2484874936/keyboard/software/groundwork/bsp_flash/bsp_flash.c

/*MIT License

Copyright (c) 2020 SEASKY-Master

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
THE SOFTWARE IS PROVIDED "AS IS", WITHOUT WARRANTY OF ANY KIND, EXPRESS OR
IMPLIED, INCLUDING BUT NOT LIMITED TO THE WARRANTIES OF MERCHANTABILITY,
FITNESS FOR A PARTICULAR PURPOSE AND NONINFRINGEMENT. IN NO EVENT SHALL THE
AUTHORS OR COPYRIGHT HOLDERS BE LIABLE FOR ANY CLAIM, DAMAGES OR OTHER
LIABILITY, WHETHER IN AN ACTION OF CONTRACT, TORT OR OTHERWISE, ARISING FROM,
OUT OF OR IN CONNECTION WITH THE SOFTWARE OR THE USE OR OTHER DEALINGS IN THE
SOFTWARE.
*/

#include "bsp_flash.h"
#include "main.h"
#include "string.h"

static uint32_t ger_sector(uint32_t address);


/**
  * @brief          擦除flash
  * @param[in]      address: flash 地址
  * @param[in]      len: 页数量
  * @retval         none
  */
void flash_erase_address(uint32_t address, uint16_t len)
{
    FLASH_EraseInitTypeDef flash_erase;
    uint32_t error;

    flash_erase.Sector = ger_sector(address);
    flash_erase.TypeErase = FLASH_TYPEERASE_SECTORS;
    flash_erase.VoltageRange = FLASH_VOLTAGE_RANGE_3;
    flash_erase.NbSectors = len;

    HAL_FLASH_Unlock();
    HAL_FLASHEx_Erase(&flash_erase, &error);
    HAL_FLASH_Lock();
}


/**
  * @brief          往一页flash写数据
  * @param[in]      start_address: flash 地址
  * @param[in]      buf: 数据指针
  * @param[in]      len: 数据长度
  * @retval         success 0, fail -1
  */
int8_t flash_write_single_address(uint32_t start_address, uint32_t *buf, uint32_t len)
{
    static uint32_t uw_address;
    static uint32_t end_address;
    static uint32_t *data_buf;
    static uint32_t data_len;

    HAL_FLASH_Unlock();

    uw_address = start_address;
    end_address = get_next_flash_address(start_address);
    data_buf = buf;
    data_len = 0;

    while (uw_address <= end_address)
    {

        if (HAL_FLASH_Program(FLASH_TYPEPROGRAM_WORD,uw_address, *data_buf) == HAL_OK)
        {
            uw_address += 4;
            data_buf++;
            data_len++;
            if (data_len == len)
            {
                break;
            }
        }
        else
        {
            HAL_FLASH_Lock();
            return -1;
        }
    }

    HAL_FLASH_Lock();
    return 0;
}


/**
  * @brief          往几页flash写数据
  * @param[in]      start_address: flash 开始地址
  * @param[in]      end_address: flash 结束地址
  * @param[in]      buf: 数据指针
  * @param[in]      len: 数据长度
  * @retval         success 0, fail -1
  */
int8_t flash_write_muli_address(uint32_t start_address, uint32_t end_address, uint32_t *buf, uint32_t len)
{
    uint32_t uw_address = 0;
    uint32_t *data_buf;
    uint32_t data_len;

    HAL_FLASH_Unlock();

    uw_address = start_address;
    data_buf = buf;
    data_len = 0;
    while (uw_address <= end_address)
    {
        if (HAL_FLASH_Program(FLASH_TYPEPROGRAM_WORD,uw_address, *data_buf) == HAL_OK)
        {
            uw_address += 4;
            data_buf++;
            data_len++;
            if (data_len == len)
            {
                break;
            }
        }
        else
        {
            HAL_FLASH_Lock();
            return -1;
        }
    }

    HAL_FLASH_Lock(); 
    return 0;
}



/**
  * @brief          从flash读数据
  * @param[in]      start_address: flash 地址
  * @param[out]     buf: 数据指针
  * @param[in]      len: 数据长度
  * @retval         none
  */
void flash_read(uint32_t address, uint32_t *buf, uint32_t len)
{
    memcpy(buf, (void*)address, len *4);
}


/**
  * @brief          获取flash的sector号
  * @param[in]      address: flash 地址
  * @retval         sector号
  */
uint32_t ger_sector(uint32_t address)
{
    uint32_t sector = 0;
    if ((address < ADDR_FLASH_SECTOR_1) && (address >= ADDR_FLASH_SECTOR_0))
    {
        sector = FLASH_SECTOR_0;
    }
    else if ((address < ADDR_FLASH_SECTOR_2) && (address >= ADDR_FLASH_SECTOR_1))
    {
        sector = FLASH_SECTOR_1;
    }
    else if ((address < ADDR_FLASH_SECTOR_3) && (address >= ADDR_FLASH_SECTOR_2))
    {
        sector = FLASH_SECTOR_2;
    }
    else if ((address < ADDR_FLASH_SECTOR_4) && (address >= ADDR_FLASH_SECTOR_3))
    {
        sector = FLASH_SECTOR_3;
    }
    else if ((address < ADDR_FLASH_SECTOR_5) && (address >= ADDR_FLASH_SECTOR_4))
    {
        sector = FLASH_SECTOR_4;
    }
    else if ((address < ADDR_FLASH_SECTOR_6) && (address >= ADDR_FLASH_SECTOR_5))
    {
        sector = FLASH_SECTOR_5;
    }
    else if ((address < ADDR_FLASH_SECTOR_7) && (address >= ADDR_FLASH_SECTOR_6))
    {
        sector = FLASH_SECTOR_6;
    }
    else if ((address < ADDR_FLASH_SECTOR_8) && (address >= ADDR_FLASH_SECTOR_7))
    {
        sector = FLASH_SECTOR_7;
    }
    else if ((address < ADDR_FLASH_SECTOR_9) && (address >= ADDR_FLASH_SECTOR_8))
    {
        sector = FLASH_SECTOR_8;
    }
    else if ((address < ADDR_FLASH_SECTOR_10) && (address >= ADDR_FLASH_SECTOR_9))
    {
        sector = FLASH_SECTOR_9;
    }
    else if ((address < ADDR_FLASH_SECTOR_11) && (address >= ADDR_FLASH_SECTOR_10))
    {
        sector = FLASH_SECTOR_10;
    }
    else if ((address < ADDR_FLASH_SECTOR_12) && (address >= ADDR_FLASH_SECTOR_11))
    {
        sector = FLASH_SECTOR_11;
    }
    else
    {
        sector = FLASH_SECTOR_11;
    }

    return sector;
}


/**
  * @brief          获取下一页flash地址
  * @param[in]      address: flash 地址
  * @retval         下一页flash地址
  */
uint32_t get_next_flash_address(uint32_t address)
{
    uint32_t sector = 0;

    if ((address < ADDR_FLASH_SECTOR_1) && (address >= ADDR_FLASH_SECTOR_0))
    {
        sector = ADDR_FLASH_SECTOR_1;
    }
    else if ((address < ADDR_FLASH_SECTOR_2) && (address >= ADDR_FLASH_SECTOR_1))
    {
        sector = ADDR_FLASH_SECTOR_2;
    }
    else if ((address < ADDR_FLASH_SECTOR_3) && (address >= ADDR_FLASH_SECTOR_2))
    {
        sector = ADDR_FLASH_SECTOR_3;
    }
    else if ((address < ADDR_FLASH_SECTOR_4) && (address >= ADDR_FLASH_SECTOR_3))
    {
        sector = ADDR_FLASH_SECTOR_4;
    }
    else if ((address < ADDR_FLASH_SECTOR_5) && (address >= ADDR_FLASH_SECTOR_4))
    {
        sector = ADDR_FLASH_SECTOR_5;
    }
    else if ((address < ADDR_FLASH_SECTOR_6) && (address >= ADDR_FLASH_SECTOR_5))
    {
        sector = ADDR_FLASH_SECTOR_6;
    }
    else if ((address < ADDR_FLASH_SECTOR_7) && (address >= ADDR_FLASH_SECTOR_6))
    {
        sector = ADDR_FLASH_SECTOR_7;
    }
    else if ((address < ADDR_FLASH_SECTOR_8) && (address >= ADDR_FLASH_SECTOR_7))
    {
        sector = ADDR_FLASH_SECTOR_8;
    }
    else if ((address < ADDR_FLASH_SECTOR_9) && (address >= ADDR_FLASH_SECTOR_8))
    {
        sector = ADDR_FLASH_SECTOR_9;
    }
    else if ((address < ADDR_FLASH_SECTOR_10) && (address >= ADDR_FLASH_SECTOR_9))
    {
        sector = ADDR_FLASH_SECTOR_10;
    }
    else if ((address < ADDR_FLASH_SECTOR_11) && (address >= ADDR_FLASH_SECTOR_10))
    {
        sector = ADDR_FLASH_SECTOR_11;
    }
    else /*(address < FLASH_END_ADDR) && (address >= ADDR_FLASH_SECTOR_23))*/
    {
        sector = FLASH_END_ADDR;
    }
    return sector;
}

//#define USER_FLASH_ADDRESS  ADDR_FLASH_SECTOR_11
//#define FLASH_DATA_LENGHT   14

//    uint8_t after_erase_data[FLASH_DATA_LENGHT];
//    uint8_t write_data[FLASH_DATA_LENGHT] = "Hello world\r\n";
//    uint8_t after_write_data[FLASH_DATA_LENGHT];
//	  //erase flash page
//    //擦除flash页
//    flash_erase_address(USER_FLASH_ADDRESS, 1);
//    //read data from flash, before writing data
//    //在写数据之前,从flash读取数据
//    flash_read(USER_FLASH_ADDRESS, (uint32_t *)after_erase_data, (FLASH_DATA_LENGHT + 3) / 4);
//    //write data to flash
//    //往flash写数据
//    flash_write_single_address(USER_FLASH_ADDRESS, (uint32_t *)write_data, (FLASH_DATA_LENGHT + 3) / 4);
//    //read data from flash, after writing data
//    //在写数据之后,从flash读取数据
//    flash_read(USER_FLASH_ADDRESS, (uint32_t *)after_write_data, (FLASH_DATA_LENGHT + 3) / 4);
