2484874936/keyboard/software/groundwork/bsp_flash/bsp_flash.h

/*MIT License

Copyright (c) 2020 SEASKY-Master

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
THE SOFTWARE IS PROVIDED "AS IS", WITHOUT WARRANTY OF ANY KIND, EXPRESS OR
IMPLIED, INCLUDING BUT NOT LIMITED TO THE WARRANTIES OF MERCHANTABILITY,
FITNESS FOR A PARTICULAR PURPOSE AND NONINFRINGEMENT. IN NO EVENT SHALL THE
AUTHORS OR COPYRIGHT HOLDERS BE LIABLE FOR ANY CLAIM, DAMAGES OR OTHER
LIABILITY, WHETHER IN AN ACTION OF CONTRACT, TORT OR OTHERWISE, ARISING FROM,
OUT OF OR IN CONNECTION WITH THE SOFTWARE OR THE USE OR OTHER DEALINGS IN THE
SOFTWARE.
*/

#ifndef BSP_FLASH_H
#define BSP_FLASH_H
#include "struct_typedef.h"

/* Base address of the Flash sectors */
#define ADDR_FLASH_SECTOR_0 ((uint32_t)0x08000000)  /* Base address of Sector 0, 16 Kbytes   */
#define ADDR_FLASH_SECTOR_1 ((uint32_t)0x08004000)  /* Base address of Sector 1, 16 Kbytes   */
#define ADDR_FLASH_SECTOR_2 ((uint32_t)0x08008000)  /* Base address of Sector 2, 16 Kbytes   */
#define ADDR_FLASH_SECTOR_3 ((uint32_t)0x0800C000)  /* Base address of Sector 3, 16 Kbytes   */
#define ADDR_FLASH_SECTOR_4 ((uint32_t)0x08010000)  /* Base address of Sector 4, 64 Kbytes   */
#define ADDR_FLASH_SECTOR_5 ((uint32_t)0x08020000)  /* Base address of Sector 5, 128 Kbytes  */
#define ADDR_FLASH_SECTOR_6 ((uint32_t)0x08040000)  /* Base address of Sector 6, 128 Kbytes  */
#define ADDR_FLASH_SECTOR_7 ((uint32_t)0x08060000)  /* Base address of Sector 7, 128 Kbytes  */
#define ADDR_FLASH_SECTOR_8 ((uint32_t)0x08080000)  /* Base address of Sector 8, 128 Kbytes  */
#define ADDR_FLASH_SECTOR_9 ((uint32_t)0x080A0000)  /* Base address of Sector 9, 128 Kbytes  */
#define ADDR_FLASH_SECTOR_10 ((uint32_t)0x080C0000) /* Base address of Sector 10, 128 Kbytes */
#define ADDR_FLASH_SECTOR_11 ((uint32_t)0x080E0000) /* Base address of Sector 11, 128 Kbytes */

#define FLASH_END_ADDR ((uint32_t)0x08100000)       /* Base address of Sector 23, 128 Kbytes */


#define ADDR_FLASH_SECTOR_12 ((uint32_t)0x08100000) /* Base address of Sector 12, 16 Kbytes  */
#define ADDR_FLASH_SECTOR_13 ((uint32_t)0x08104000) /* Base address of Sector 13, 16 Kbytes  */
#define ADDR_FLASH_SECTOR_14 ((uint32_t)0x08108000) /* Base address of Sector 14, 16 Kbytes  */
#define ADDR_FLASH_SECTOR_15 ((uint32_t)0x0810C000) /* Base address of Sector 15, 16 Kbytes  */
#define ADDR_FLASH_SECTOR_16 ((uint32_t)0x08110000) /* Base address of Sector 16, 64 Kbytes  */
#define ADDR_FLASH_SECTOR_17 ((uint32_t)0x08120000) /* Base address of Sector 17, 128 Kbytes */
#define ADDR_FLASH_SECTOR_18 ((uint32_t)0x08140000) /* Base address of Sector 18, 128 Kbytes */
#define ADDR_FLASH_SECTOR_19 ((uint32_t)0x08160000) /* Base address of Sector 19, 128 Kbytes */
#define ADDR_FLASH_SECTOR_20 ((uint32_t)0x08180000) /* Base address of Sector 20, 128 Kbytes */
#define ADDR_FLASH_SECTOR_21 ((uint32_t)0x081A0000) /* Base address of Sector 21, 128 Kbytes */
#define ADDR_FLASH_SECTOR_22 ((uint32_t)0x081C0000) /* Base address of Sector 22, 128 Kbytes */
#define ADDR_FLASH_SECTOR_23 ((uint32_t)0x081E0000) /* Base address of Sector 23, 128 Kbytes */



/**
  * @brief          erase flash
  * @param[in]      address: flash address
  * @param[in]      len: page num
  * @retval         none
  */
/**
  * @brief          擦除flash
  * @param[in]      address: flash 地址
  * @param[in]      len: 页数量
  * @retval         none
  */
extern void flash_erase_address(uint32_t address, uint16_t len);

/**
  * @brief          write data to one page of flash
  * @param[in]      start_address: flash address
  * @param[in]      buf: data point
  * @param[in]      len: data num
  * @retval         success 0, fail -1
  */
/**
  * @brief          往一页flash写数据
  * @param[in]      start_address: flash 地址
  * @param[in]      buf: 数据指针
  * @param[in]      len: 数据长度
  * @retval         success 0, fail -1
  */
extern int8_t flash_write_single_address(uint32_t start_address, uint32_t *buf, uint32_t len);


/**
  * @brief          write data to some pages of flash
  * @param[in]      start_address: flash start address
  * @param[in]      end_address: flash end address
  * @param[in]      buf: data point
  * @param[in]      len: data num
  * @retval         success 0, fail -1
  */
/**
  * @brief          往几页flash写数据
  * @param[in]      start_address: flash 开始地址
  * @param[in]      end_address: flash 结束地址
  * @param[in]      buf: 数据指针
  * @param[in]      len: 数据长度
  * @retval         success 0, fail -1
  */
extern int8_t flash_write_muli_address(uint32_t start_address, uint32_t end_address, uint32_t *buf, uint32_t len);

/**
  * @brief          read data for flash
  * @param[in]      address: flash address
  * @param[out]     buf: data point
  * @param[in]      len: data num
  * @retval         none
  */
/**
  * @brief          从flash读数据
  * @param[in]      start_address: flash 地址
  * @param[out]     buf: 数据指针
  * @param[in]      len: 数据长度
  * @retval         none
  */
extern void flash_read(uint32_t address, uint32_t *buf, uint32_t len);

/**
  * @brief          get the sector number of flash
  * @param[in]      address: flash address
  * @retval         sector number
  */
/**
  * @brief          获取flash的sector号
  * @param[in]      address: flash 地址
  * @retval         sector号
  */
extern uint32_t ger_sector(uint32_t address);
/**
  * @brief          get the next page flash address
  * @param[in]      address: flash address
  * @retval         next page flash address
  */
/**
  * @brief          获取下一页flash地址
  * @param[in]      address: flash 地址
  * @retval         下一页flash地址
  */
extern uint32_t get_next_flash_address(uint32_t address);
#endif
