2484874936/keyboard/software/Src/usart.c

/**
  ******************************************************************************
  * File Name          : USART.c
  * Description        : This file provides code for the configuration
  *                      of the USART instances.
  ******************************************************************************
  * @attention
  *
  * <h2><center>&copy; Copyright (c) 2020 STMicroelectronics.
  * All rights reserved.</center></h2>
  *
  * This software component is licensed by ST under Ultimate Liberty license
  * SLA0044, the "License"; You may not use this file except in compliance with
  * the License. You may obtain a copy of the License at:
  *                             www.st.com/SLA0044
  *
  ******************************************************************************
  */

/* Includes ------------------------------------------------------------------*/
#include "usart.h"

/* USER CODE BEGIN 0 */
#if 1
#pragma import(__use_no_semihosting)             
//标准库需要的支持函数                 
struct __FILE 
{ 
	int handle; 
}; 

FILE __stdout;       
//定义_sys_exit()以避免使用半主机模式    
void _sys_exit(int x) 
{ 
	x = x; 
} 
//重定义fputc函数 
int fputc(int ch, FILE *f)
{ 	
	while((UART4->SR&0X40)==0);//循环发送,直到发送完毕   
	UART4->DR = (uint8_t) ch;      
	return ch;
}
#endif 
/* USER CODE END 0 */

UART_HandleTypeDef huart4;
UART_HandleTypeDef huart5;
UART_HandleTypeDef huart1;
UART_HandleTypeDef huart3;

/* UART4 init function */
void MX_UART4_Init(void)
{

  huart4.Instance = UART4;
  huart4.Init.BaudRate = 9600;
  huart4.Init.WordLength = UART_WORDLENGTH_8B;
  huart4.Init.StopBits = UART_STOPBITS_1;
  huart4.Init.Parity = UART_PARITY_NONE;
  huart4.Init.Mode = UART_MODE_TX_RX;
  huart4.Init.HwFlowCtl = UART_HWCONTROL_NONE;
  huart4.Init.OverSampling = UART_OVERSAMPLING_16;
  if (HAL_UART_Init(&huart4) != HAL_OK)
  {
    Error_Handler();
  }

}
/* UART5 init function */
void MX_UART5_Init(void)
{
  huart5.Instance = UART5;
  huart5.Init.BaudRate = 115200;
  huart5.Init.WordLength = UART_WORDLENGTH_8B;
  huart5.Init.StopBits = UART_STOPBITS_1;
  huart5.Init.Parity = UART_PARITY_NONE;
  huart5.Init.Mode = UART_MODE_TX_RX;
  huart5.Init.HwFlowCtl = UART_HWCONTROL_NONE;
  huart5.Init.OverSampling = UART_OVERSAMPLING_16;
  if (HAL_UART_Init(&huart5) != HAL_OK)
  {
    Error_Handler();
  }

}
/* USART1 init function */

void MX_USART1_UART_Init(void)
{

  huart1.Instance = USART1;
  huart1.Init.BaudRate = 115200;
  huart1.Init.WordLength = UART_WORDLENGTH_8B;
  huart1.Init.StopBits = UART_STOPBITS_1;
  huart1.Init.Parity = UART_PARITY_NONE;
  huart1.Init.Mode = UART_MODE_TX_RX;
  huart1.Init.HwFlowCtl = UART_HWCONTROL_NONE;
  huart1.Init.OverSampling = UART_OVERSAMPLING_16;
  if (HAL_UART_Init(&huart1) != HAL_OK)
  {
    Error_Handler();
  }

}
/* USART3 init function */

void MX_USART3_UART_Init(void)
{

  huart3.Instance = USART3;
  huart3.Init.BaudRate = 115200;
  huart3.Init.WordLength = UART_WORDLENGTH_8B;
  huart3.Init.StopBits = UART_STOPBITS_1;
  huart3.Init.Parity = UART_PARITY_NONE;
  huart3.Init.Mode = UART_MODE_TX_RX;
  huart3.Init.HwFlowCtl = UART_HWCONTROL_NONE;
  huart3.Init.OverSampling = UART_OVERSAMPLING_16;
  if (HAL_UART_Init(&huart3) != HAL_OK)
  {
    Error_Handler();
  }

}

void HAL_UART_MspInit(UART_HandleTypeDef* uartHandle)
{

  GPIO_InitTypeDef GPIO_InitStruct = {0};
  if(uartHandle->Instance==UART4)
  {
    /* UART4 clock enable */
    __HAL_RCC_UART4_CLK_ENABLE();
  
    __HAL_RCC_GPIOA_CLK_ENABLE();
    /**UART4 GPIO Configuration    
    PA0-WKUP     ------> UART4_TX
    PA1     ------> UART4_RX 
    */
    GPIO_InitStruct.Pin = GPIO_PIN_0|GPIO_PIN_1;
    GPIO_InitStruct.Mode = GPIO_MODE_AF_PP;
    GPIO_InitStruct.Pull = GPIO_PULLUP;
    GPIO_InitStruct.Speed = GPIO_SPEED_FREQ_VERY_HIGH;
    GPIO_InitStruct.Alternate = GPIO_AF8_UART4;
    HAL_GPIO_Init(GPIOA, &GPIO_InitStruct);

  }
  else if(uartHandle->Instance==UART5)
  {
    /* UART5 clock enable */
    __HAL_RCC_UART5_CLK_ENABLE();
  
    __HAL_RCC_GPIOC_CLK_ENABLE();
    __HAL_RCC_GPIOD_CLK_ENABLE();
    /**UART5 GPIO Configuration    
    PC12     ------> UART5_TX
    PD2     ------> UART5_RX 
    */
    GPIO_InitStruct.Pin = GPIO_PIN_12;
    GPIO_InitStruct.Mode = GPIO_MODE_AF_PP;
    GPIO_InitStruct.Pull = GPIO_PULLUP;
    GPIO_InitStruct.Speed = GPIO_SPEED_FREQ_VERY_HIGH;
    GPIO_InitStruct.Alternate = GPIO_AF8_UART5;
    HAL_GPIO_Init(GPIOC, &GPIO_InitStruct);

    GPIO_InitStruct.Pin = GPIO_PIN_2;
    GPIO_InitStruct.Mode = GPIO_MODE_AF_PP;
    GPIO_InitStruct.Pull = GPIO_PULLUP;
    GPIO_InitStruct.Speed = GPIO_SPEED_FREQ_VERY_HIGH;
    GPIO_InitStruct.Alternate = GPIO_AF8_UART5;
    HAL_GPIO_Init(GPIOD, &GPIO_InitStruct);

  }
  else if(uartHandle->Instance==USART1)
  {
    /* USART1 clock enable */
    __HAL_RCC_USART1_CLK_ENABLE();
  
    __HAL_RCC_GPIOA_CLK_ENABLE();
    /**USART1 GPIO Configuration    
    PA9     ------> USART1_TX
    PA10     ------> USART1_RX 
    */
    GPIO_InitStruct.Pin = GPIO_PIN_9|GPIO_PIN_10;
    GPIO_InitStruct.Mode = GPIO_MODE_AF_PP;
    GPIO_InitStruct.Pull = GPIO_NOPULL;
    GPIO_InitStruct.Speed = GPIO_SPEED_FREQ_VERY_HIGH;
    GPIO_InitStruct.Alternate = GPIO_AF7_USART1;
    HAL_GPIO_Init(GPIOA, &GPIO_InitStruct);

  }
  else if(uartHandle->Instance==USART3)
  {
    /* USART3 clock enable */
    __HAL_RCC_USART3_CLK_ENABLE();
  
    __HAL_RCC_GPIOC_CLK_ENABLE();
    /**USART3 GPIO Configuration    
    PC10     ------> USART3_TX
    PC11     ------> USART3_RX 
    */
    GPIO_InitStruct.Pin = GPIO_PIN_10|GPIO_PIN_11;
    GPIO_InitStruct.Mode = GPIO_MODE_AF_PP;
    GPIO_InitStruct.Pull = GPIO_NOPULL;
    GPIO_InitStruct.Speed = GPIO_SPEED_FREQ_VERY_HIGH;
    GPIO_InitStruct.Alternate = GPIO_AF7_USART3;
    HAL_GPIO_Init(GPIOC, &GPIO_InitStruct);

  }
}

void HAL_UART_MspDeInit(UART_HandleTypeDef* uartHandle)
{

  if(uartHandle->Instance==UART4)
  {
    /* Peripheral clock disable */
    __HAL_RCC_UART4_CLK_DISABLE();
  
    /**UART4 GPIO Configuration    
    PA0-WKUP     ------> UART4_TX
    PA1     ------> UART4_RX 
    */
    HAL_GPIO_DeInit(GPIOA, GPIO_PIN_0|GPIO_PIN_1);

  }
  else if(uartHandle->Instance==UART5)
  {
    /* Peripheral clock disable */
    __HAL_RCC_UART5_CLK_DISABLE();
  
    /**UART5 GPIO Configuration    
    PC12     ------> UART5_TX
    PD2     ------> UART5_RX 
    */
    HAL_GPIO_DeInit(GPIOC, GPIO_PIN_12);

    HAL_GPIO_DeInit(GPIOD, GPIO_PIN_2);

  }
  else if(uartHandle->Instance==USART1)
  {
    /* Peripheral clock disable */
    __HAL_RCC_USART1_CLK_DISABLE();
  
    /**USART1 GPIO Configuration    
    PA9     ------> USART1_TX
    PA10     ------> USART1_RX 
    */
    HAL_GPIO_DeInit(GPIOA, GPIO_PIN_9|GPIO_PIN_10);

  }
  else if(uartHandle->Instance==USART3)
  {
    /* Peripheral clock disable */
    __HAL_RCC_USART3_CLK_DISABLE();
  
    /**USART3 GPIO Configuration    
    PC10     ------> USART3_TX
    PC11     ------> USART3_RX 
    */
    HAL_GPIO_DeInit(GPIOC, GPIO_PIN_10|GPIO_PIN_11);

  }
} 

/************************ (C) COPYRIGHT STMicroelectronics *****END OF FILE****/
