2484874936/keyboard/software/Src/tim.c

/**
  ******************************************************************************
  * File Name          : TIM.c
  * Description        : This file provides code for the configuration
  *                      of the TIM instances.
  ******************************************************************************
  * @attention
  *
  * <h2><center>&copy; Copyright (c) 2020 STMicroelectronics.
  * All rights reserved.</center></h2>
  *
  * This software component is licensed by ST under Ultimate Liberty license
  * SLA0044, the "License"; You may not use this file except in compliance with
  * the License. You may obtain a copy of the License at:
  *                             www.st.com/SLA0044
  *
  ******************************************************************************
  */

/* Includes ------------------------------------------------------------------*/
#include "tim.h"

/* USER CODE BEGIN 0 */
#include "bsp_ws2812b.h"
#include "ws2812b_task.h"

extern void mx_ws2812b_IRQHandler(keyboard_rgb *board_rgb_led);
extern keyboard_rgb board_rgb[87];
/*
1.2us -- 0.833MHz
需要配置小于 0.83MHz
TIM4-APB1 42MHz->84MHz
PSC（7-1） ->  12MHz
ARR (24-1)   -> 0.5MHz
*/
/* USER CODE END 0 */

TIM_HandleTypeDef htim4;

/* TIM4 init function */
void MX_TIM4_Init(void)
{
  TIM_ClockConfigTypeDef sClockSourceConfig = {0};
  TIM_MasterConfigTypeDef sMasterConfig = {0};
  TIM_OC_InitTypeDef sConfigOC = {0};

  htim4.Instance = TIM4;
  htim4.Init.Prescaler = 6;
  htim4.Init.CounterMode = TIM_COUNTERMODE_UP;
  htim4.Init.Period = 23;
  htim4.Init.ClockDivision = TIM_CLOCKDIVISION_DIV1;
  htim4.Init.AutoReloadPreload = TIM_AUTORELOAD_PRELOAD_ENABLE;
  if (HAL_TIM_Base_Init(&htim4) != HAL_OK)
  {
    Error_Handler();
  }
  sClockSourceConfig.ClockSource = TIM_CLOCKSOURCE_INTERNAL;
  if (HAL_TIM_ConfigClockSource(&htim4, &sClockSourceConfig) != HAL_OK)
  {
    Error_Handler();
  }
  if (HAL_TIM_PWM_Init(&htim4) != HAL_OK)
  {
    Error_Handler();
  }
  sMasterConfig.MasterOutputTrigger = TIM_TRGO_RESET;
  sMasterConfig.MasterSlaveMode = TIM_MASTERSLAVEMODE_DISABLE;
  if (HAL_TIMEx_MasterConfigSynchronization(&htim4, &sMasterConfig) != HAL_OK)
  {
    Error_Handler();
  }
  sConfigOC.OCMode = TIM_OCMODE_PWM1;
  sConfigOC.Pulse = 12;
  sConfigOC.OCPolarity = TIM_OCPOLARITY_HIGH;
  sConfigOC.OCFastMode = TIM_OCFAST_DISABLE;
  if (HAL_TIM_PWM_ConfigChannel(&htim4, &sConfigOC, TIM_CHANNEL_2) != HAL_OK)
  {
    Error_Handler();
  }
  if (HAL_TIM_PWM_ConfigChannel(&htim4, &sConfigOC, TIM_CHANNEL_3) != HAL_OK)
  {
    Error_Handler();
  }
  if (HAL_TIM_PWM_ConfigChannel(&htim4, &sConfigOC, TIM_CHANNEL_4) != HAL_OK)
  {
    Error_Handler();
  }
  HAL_TIM_MspPostInit(&htim4);

}

void HAL_TIM_Base_MspInit(TIM_HandleTypeDef* tim_baseHandle)
{

  if(tim_baseHandle->Instance==TIM4)
  {
    /* TIM4 clock enable */
    __HAL_RCC_TIM4_CLK_ENABLE();

    /* TIM4 interrupt Init */
    HAL_NVIC_SetPriority(TIM4_IRQn, 5, 0);
    HAL_NVIC_EnableIRQ(TIM4_IRQn);
  }
}
void HAL_TIM_MspPostInit(TIM_HandleTypeDef* timHandle)
{

  GPIO_InitTypeDef GPIO_InitStruct = {0};
  if(timHandle->Instance==TIM4)
  {
  
    __HAL_RCC_GPIOB_CLK_ENABLE();
    /**TIM4 GPIO Configuration    
    PB7     ------> TIM4_CH2
    PB8     ------> TIM4_CH3
    PB9     ------> TIM4_CH4 
    */
    GPIO_InitStruct.Pin = DIN_3V3_1_Pin|DIN_3V3_2_Pin|DIN_3V3_3_Pin;
    GPIO_InitStruct.Mode = GPIO_MODE_AF_PP;
    GPIO_InitStruct.Pull = GPIO_PULLDOWN;
    GPIO_InitStruct.Speed = GPIO_SPEED_FREQ_VERY_HIGH;
    GPIO_InitStruct.Alternate = GPIO_AF2_TIM4;
    HAL_GPIO_Init(GPIOB, &GPIO_InitStruct);

  }

}

void HAL_TIM_Base_MspDeInit(TIM_HandleTypeDef* tim_baseHandle)
{

  if(tim_baseHandle->Instance==TIM4)
  {
    /* Peripheral clock disable */
    __HAL_RCC_TIM4_CLK_DISABLE();

    /* TIM4 interrupt Deinit */
    HAL_NVIC_DisableIRQ(TIM4_IRQn);
  }
} 

/* USER CODE BEGIN 1 */
uint8_t time;
//void HAL_TIM_PeriodElapsedCallback(TIM_HandleTypeDef *htim)
void TIM4_IRQHandler(void)
{
    if (__HAL_TIM_GET_FLAG(&htim4, TIM_FLAG_UPDATE) != RESET)
        {
            if (__HAL_TIM_GET_IT_SOURCE(&htim4, TIM_IT_UPDATE) != RESET)
                {
                    __HAL_TIM_CLEAR_IT(&htim4, TIM_IT_UPDATE);
//					mx_ws2812b_IRQHandler(board_rgb);
					ws2812b_IRQ();
                }
        }
}
/* USER CODE END 1 */

/************************ (C) COPYRIGHT STMicroelectronics *****END OF FILE****/
